gimme1dollar/vision_ai_kiosk/firmware/Core/Inc/RTE_Components.h

/**
  ******************************************************************************
  * @file
  * @author  MCD Application Team
  * @version V2.0.0
  ******************************************************************************
  * @attention
  *
  * COPYRIGHT(c) 2021 STMicroelectronics
  *
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
  */
  /* Define to prevent recursive inclusion -------------------------------------*/
#ifndef  __RTE_COMPONENTS_H__
#define  __RTE_COMPONENTS_H__

/* Defines ------------------------------------------------------------------*/
/* STMicroelectronics.X-CUBE-AI.5.2.0 */
#define AI_ApplicationTemplate

#endif /* __RTE_COMPONENTS_H__ */
